dongyulnx-ctrl/gait-analysis-wearable/hardware/embedded/USART/USER/AllHeader.h

#ifndef __ALLHEADER_H
#define __ALLHEADER_H


//ͷ�ļ�	Header Files
#include <stdio.h>
#include <string.h>
#include <stdlib.h>
#include <math.h>
#include <stdbool.h>


#include "stm32f10x.h"
#include "stm32f10x_gpio.h"

#include "myenum.h"

#include "delay.h"
#include "bsp.h"
#include "usart.h"

#include "imu_uart_driver.h"
#include "bsp_timer.h"



#endif
